pawlex/poor86-dev/docs/DECISIONS.md

# Design decisions

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

Two conventions carried throughout:

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

## Decided: one soldered CPU, SX-class bus, 3.3 V

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

### What follows

```
  one SX-class CPU  ->  16-bit data, 24-bit address
                    ->  no PCI (32-bit, anachronistic)
                    ->  no VL-Bus slot; local-bus video still fine
                    ->  ISA-class programming model
                    ->  16 MiB guest RAM ceiling
```

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

### 3.3 V is the important part

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

### Why SL/SLC is a good fit beyond the voltage

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

### The 486 part: Am5x86-133

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

### ...and it brings the hardest chipset problem

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

What the chipset has to deal with that an SX-class bus does not:

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

Three ways out, in increasing order of cost:

1. **Never assert `KEN#`.** External memory is uncacheable, the L1 is
   effectively disabled, coherency evaporates. Simplest possible chipset
   — and throws away most of what the 133 MHz part was bought for.
2. **Cacheable but no burst.** Assert `KEN#`, answer each of the four
   transfers with a normal ready rather than `BRDY#`. Line fills cost 4
   cycles instead of a burst, but the cache works. Still needs a
   coherency answer.
3. **Selective cacheability plus snooping.** `KEN#` asserted only for
   regions no other agent writes, snooping via `AHOLD`/`EADS#` for the
   rest. Fastest and hardest.

Note (1) and (2) make the *coherency* question mostly disappear, which is
worth weighing: the difficulty is not evenly distributed across the
options.

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

### The risk this sequencing creates, and the cheap insurance

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

### Two CPU options: a bitstream difference, and a footprint problem

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

### The soft core's role varies by SKU — and that has a consequence

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

### Consequences worth recording

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

## Decided: no PCI (follows from the above)

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

### The evidence

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

```
addr=00000000fffe0000 size=0x020000 mem=ram name="bios.bin"
...
Detected non-PCI system
ATA controller 1 at 1f0/3f4/0 (irq 14 dev ffffffff)
ATA controller 2 at 170/374/0 (irq 15 dev ffffffff)
Running option rom at c000:0003            <- ISA VGA
DVD/CD [ata1-0: QEMU DVD-ROM ATAPI-4 DVD/CD]
```

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

### Correction: this supersedes the `bios-geometry` plan

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

```c
int boot_lchs_find_ata_device(struct pci_device *pci, ...)
{
    if (!CONFIG_HOST_BIOS_GEOMETRY) return -1;
    if (!pci) return -1;      // support only pci machine for now
```

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

- [ ] Drop `bios-geometry` from the reset-image plan; keep `bootorder`,
      which does not depend on PCI.

## Video: HDMI on-board, framebuffer in external DRAM

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

### Two video paths, and they are alternatives worth keeping distinct

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

Three things to check early:

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

### Direction: be register-compatible with QEMU's Cirrus model

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

Plus a standard VGA core underneath, which `stdvga.c` drives.

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

- [ ] Decide which Cirrus the model claims to be, and make sequencer
      `0x0f` report a size that matches the DRAM actually allocated.
- [ ] **Place `vgabios-cirrus.bin` at `0xc0000`.** With no PCI there is
      no expansion-ROM BAR, so the BIOS finds it by scanning — which is
      exactly what `isapc` does (`Running option rom at c000:0003`).
      That makes the VGA BIOS another reset-vector-placed image.
- [ ] Decide whether BitBLT is ever in scope, or explicitly out.

## Decided in principle: sound synthesis is software

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

Two reasons, and the second is the stronger one:

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

## OPEN, and blocking: the dividing line between the two controllers

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

### Three tiers, not two

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

### Split each peripheral at the register interface

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

### What decides it

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

### First-pass reading, to be confirmed rather than assumed

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

### The testbench can answer this empirically

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

- [ ] Determine the dividing line. Until then the arbitration items
      below stay open on purpose.

## Design goal: mini-ITX form factor

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

### The tension worth resolving: a physical VLB slot does not fit

Approximate edge budget against 170 mm:

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

### Other things the form factor decides

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

## Design goal: reduced BOM at the motherboard layer

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

### Two controllers, not one

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

This costs no parts, which is consistent with the goal above.

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

## Decided: firmware configuration goes over fw_cfg, not CMOS

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

The CMOS device stays for time and the shutdown status byte.

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

## Decided: CMOS is a compatibility surface, populated at reset-exit

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

### What the RTL block is

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

### Persistence: an ESP32 on the board, not a coin cell

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

### One control channel: controller -> chipset -> fw_cfg -> SeaBIOS

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

A useful consequence already visible in the model: advertised RAM need
not equal fitted RAM.

### Population: a chipset reset-exit initialisation vector

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

## Decided: block storage is backed by the ESP32

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

Nothing has to wait for IDENTIFY, and no SeaBIOS patch is needed.

Open:

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

### Storage back end: the physical stores — OPEN, parked

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

#### Tier 1 may need no new part

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

#### The real question: is the config ROM also bulk storage?

Measured on the actual part — LFE5U-85F, `ecppack`:

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

**What the config ROM should and should not carry:**

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

#### 64 MiB NOR is readily available, and 56 MiB changes the role

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

#### Tier 2: SD is slower than it needs to be, which is fine

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

#### Tier 2 as cache is what makes tier 3 safe

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

#### Image selection: in-band and out-of-band both have a use

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

### ATAPI CD-ROM: emulated by the controller, network-backed (TBD)

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

Two things already settled in our favour:

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

Two things to watch:

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

## Decided: networking is NE2000, serviced by the ESP32

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

```c
#else
    esp_read_mac(s->macaddr, ESP_MAC_WIFI_STA);
#endif
```

So the intended hardware arrangement is already implemented upstream.

Open:

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

## Design goal: modern memory — which makes the cache the central choice

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

Two characteristics are wanted:

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

### The mismatch, stated plainly

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

### The trap

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

Some rough calibration, illustrative rather than exact:

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

### Why the cache is therefore the important design choice

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

### What a cache costs to build here, measured

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

### ao486's role here: traffic generator, not bus model

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

### Candidates already in the tree

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

The right answer depends on the cache, which is the point of this
section.

### External evidence: M8SBC-486

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

Read from its constraints file and chipset sources:

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

### Decided: the cache data array lives in FPGA block RAM

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

Two things fall out neatly:

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

### And this is the real justification for deferring the memory subsystem

The deferral is recorded elsewhere as discipline — not starting with the
most interesting part, so the surrounding work gets finished. **That is
true but it is the weaker reason. The stronger one is that the ordering
is simply correct.**

The dependency runs one way:

```
  CPU latency budget   (fixed -- the CPU is chosen)
        |
        v
  cache: line size, associativity, write policy
        |
        v
  memory subsystem     (the free variable)
```

The memory subsystem is **downstream of the cache, which is downstream
of a latency budget set by the CPU.** Specifying it first means
optimising a component before its requirements exist — and the instinct
one optimises on, bandwidth, is precisely the one that hurts here.

The failure mode is concrete and worth naming: **a high-bandwidth memory
subsystem that cripples the bus interface with latency.** Deep
pipelining, transaction reordering, long bursts and elaborate scheduling
all improve throughput and all delay the first word. If the BIU cannot
hide that — because the cache is small, or the line size is mismatched,
or a region is deliberately uncached — the result is better memory
numbers and a slower machine. It would be entirely possible to build
something impressive in isolation that makes this machine worse.

So the memory subsystem is not being avoided. **It is waiting for its
requirements**, which do not exist until the CPU-side budget is
established and the cache is designed.

### The four-word ceiling inverts the usual choice

**A 486 burst is four transfers. Sixteen bytes. That is the entire
amortisation window**, and there is nothing longer anywhere in the
machine — the SX has no burst at all.

A memory part with a long fixed setup cost cannot amortise it across
four words; the setup simply dominates every access. Which means the
usual instinct — pick the part with the best sustained bandwidth — is
backwards here. **Low latency beats high bandwidth, and it is not close.**

That likely favours **parallel SRAM or parallel PSRAM**: more pins, no
row activation to hide, access latency close to the CPU's own budget.
And it likely disfavours HyperRAM, whose pin efficiency is attractive
against an FPGA I/O budget but whose high initial latency wants long
bursts that this machine will never issue.

Capacity is not the constraint it would normally be. A 386SX cannot
address beyond 16 MiB at all, and a DOS machine wants single-digit
megabytes — so the usual reason to accept latency in exchange for
density does not apply either.

### Supporting the SX roughly doubles the work here

The cost of SX support was first recorded as a second *bus* front end.
**The memory subsystem is the larger half**, and it was not visible at
the time:

| | access pattern |
|---|---|
| 386SX | single 16-bit transfers, **no burst at all** |
| Am5x86 | four-transfer 32-bit line fills, single cycles otherwise |

A controller tuned for one is not tuned for the other — different width,
different burst behaviour, and quite possibly a different cache design,
since the question of whether the SX path gets a cache at all is
separate.

**The open question, and it is genuinely open:**

- **One subsystem serving both.** One design, one validation, and
  optimal for neither — compromised on width, line size and fill policy.
- **Two paths.** Each right for its CPU, twice the design and twice the
  validation. The difference between them is itself worth understanding,
  and this is the part of the project the author actually wants to build.
- **A third framing worth testing before choosing:** this is programmable
  logic, so "two paths" may be two *configurations* of one parameterised
  design rather than two designs — the same argument already made for
  the bus front end. Whether that holds depends on how much of the
  difference is parameter (width, burst length, line size) and how much
  is structure. Worth establishing early, because it decides whether the
  cost is 2x or closer to 1.2x.

- [ ] **Decide whether the SX is supported**, knowing the memory
      subsystem cost and not only the bus front-end cost.
- [ ] Establish the latency budget from the CPU side first. It is the
      fixed constraint; bandwidth is the free variable.
- [ ] Design the cache against that budget — line size, associativity,
      write policy.
- [ ] *Then* define what "modern memory" means concretely, and match its
      efficient burst length to the line size already chosen.
